sjbar03/XCKU5P-Development-Notes/Spice/2bitdac.asc

R1: res; 840
R2: res; 420
R4: res; 75
V2: voltage; PULSE(0 3.3 20m 0 0 20m 40m 2)
V3: voltage; PULSE(0 3.3 10m 0 0 10m 20m 4)
Named nets: 0, OUT
.tran 1000m
