sjbar03/XCKU5P-Development-Notes/Spice/3bit-ladder-dac.asc

R2: res; {2*R}
R3: res; {2*R}
R4: res; {2*R}
R5: res; {2*R}
R6: res; {R}
R7: res; {R}
R8: Res; {D1}
R9: Res; {D2}
VGPIO0: voltage; PULSE(0 3.3 0 1n 1n 4u 8u)
VGPIO1: voltage; PULSE(0 3.3 0 1n 1n 2u 4u)
VGPIO2: voltage; PULSE(0 3.3 0 1n 1n 1u 2u)
Named nets: 0, VOUT
.param R=1k D1=1.7k D2=1k
.tran 10n 8u
